moretticam/SystemVerilog-SUMOBOT/Sumo_Robot_Media/IMG_20260503_175123.jpg

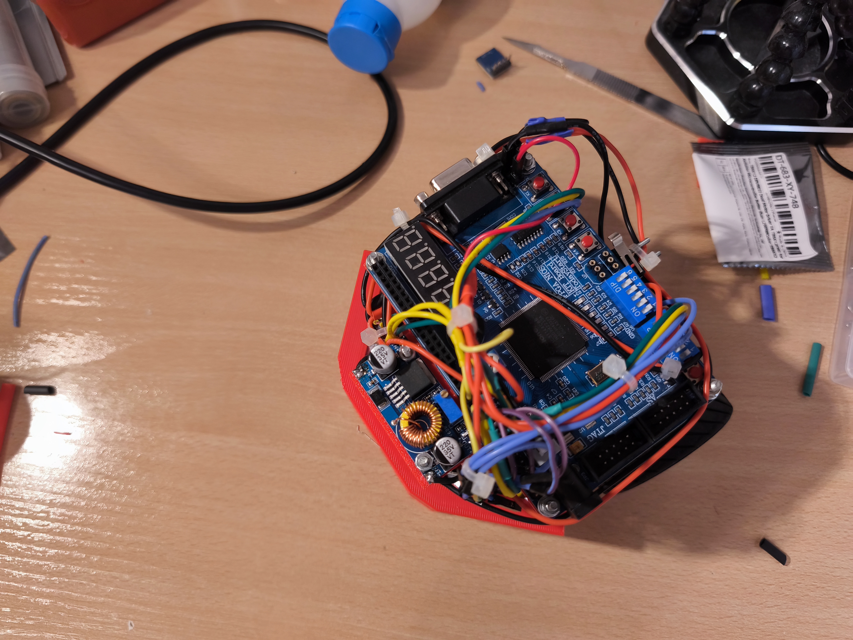
Sumo_Robot_Media/IMG_20260503_175123.jpg
